jameskan1011/EMG-Controlled-Prosthetic-Hand/3D model/plunger/socket.SLDPRT

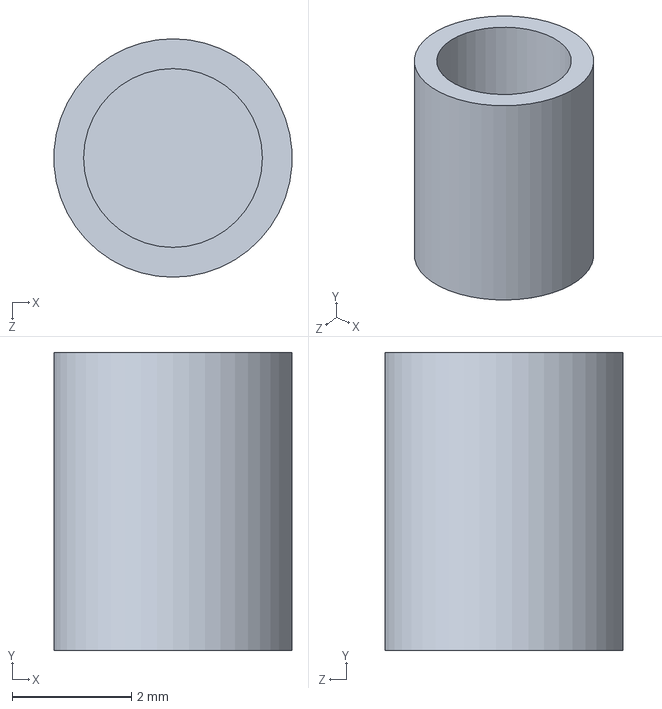
[picture p16: CAD file, 2025-07-29]
3D model/plunger/socket.SLDPRT
3.99 x 5.00 x 4.00 mm
