jameskan1011/EMG-Controlled-Prosthetic-Hand/3D model/thumb/bambu/Thump1.3MF

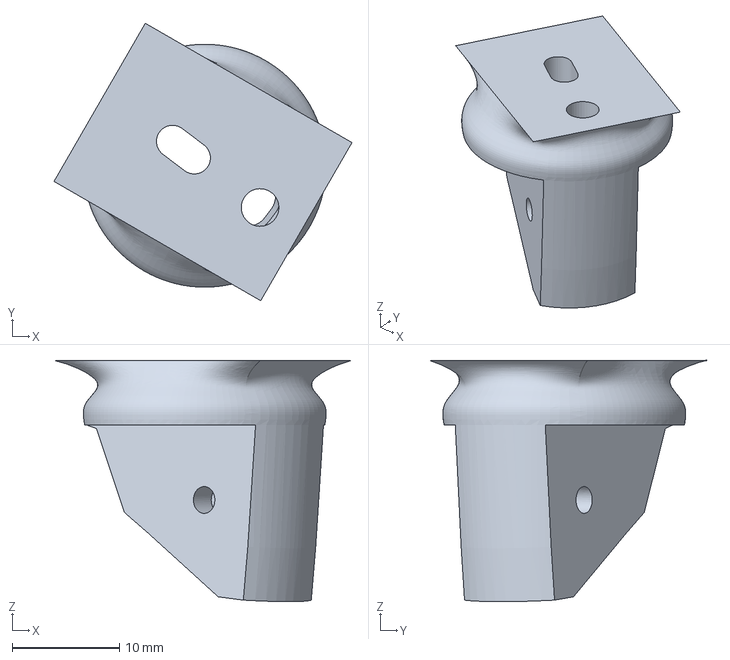
[picture p17: CAD file, 2025-07-29]
3D model/thumb/bambu/Thump1.3MF
27.7 x 25.8 x 22.5 mm
