jameskan1011/EMG-Controlled-Prosthetic-Hand/3D model/thumb/thump4.SLDPRT

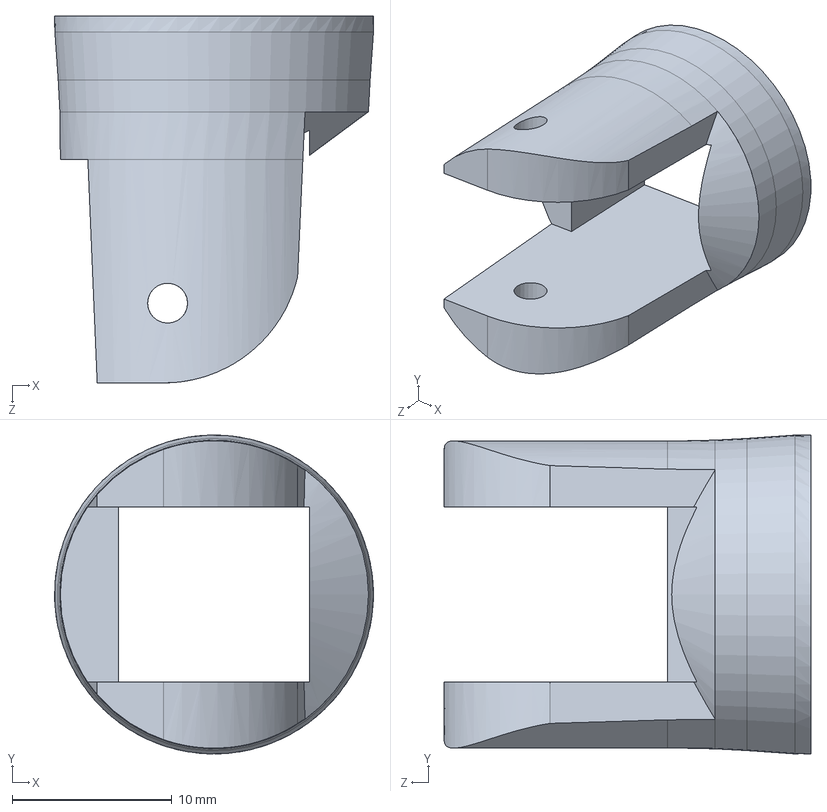
[picture p18: CAD file, 2025-07-29]
3D model/thumb/thump4.SLDPRT
20.0 x 20.0 x 23.0 mm
