jameskan1011/EMG-Controlled-Prosthetic-Hand/3D model/2051_servo_tower-pro-sg90.pk2.SLDPRT

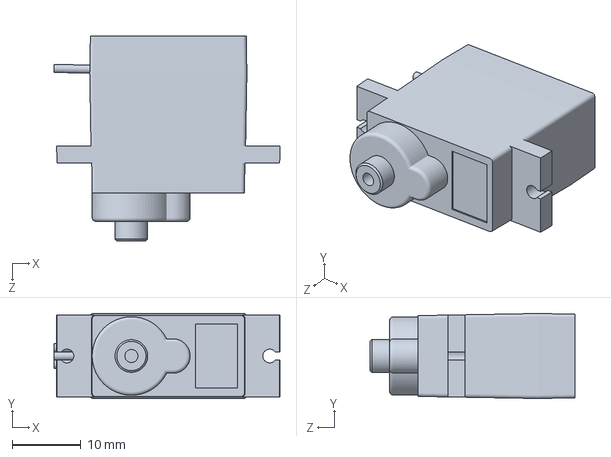
[picture p19: CAD file, 2025-07-29]
3D model/2051_servo_tower-pro-sg90.pk2.SLDPRT
32.9 x 12.4 x 29.8 mm
