jameskan1011/EMG-Controlled-Prosthetic-Hand/3D model/ESP32_enclosure/ESP32_enclosure.SLDPRT

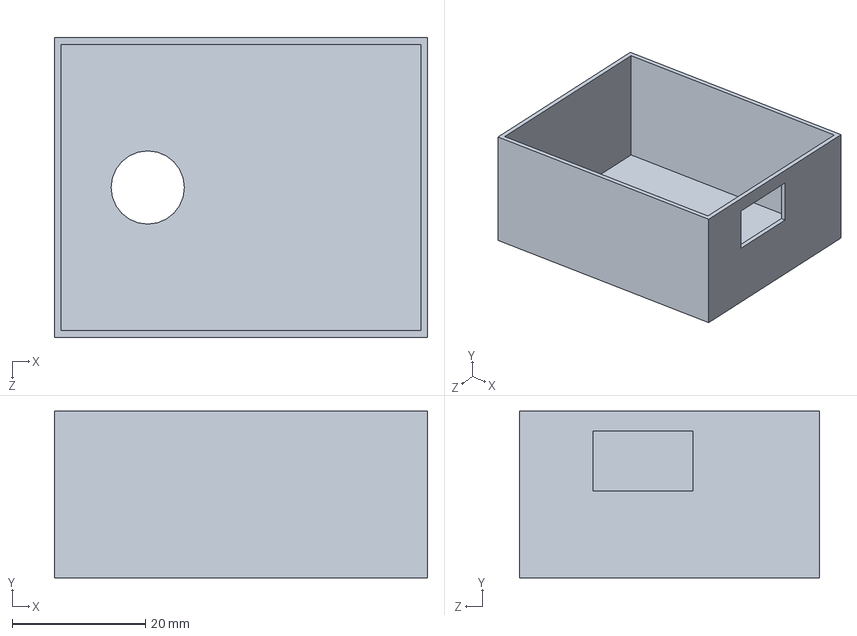
[picture p20: CAD file, 2025-07-29]
3D model/ESP32_enclosure/ESP32_enclosure.SLDPRT
56.0 x 25.0 x 45.0 mm
