jameskan1011/EMG-Controlled-Prosthetic-Hand/3D model/pinky/pinky3.SLDPRT

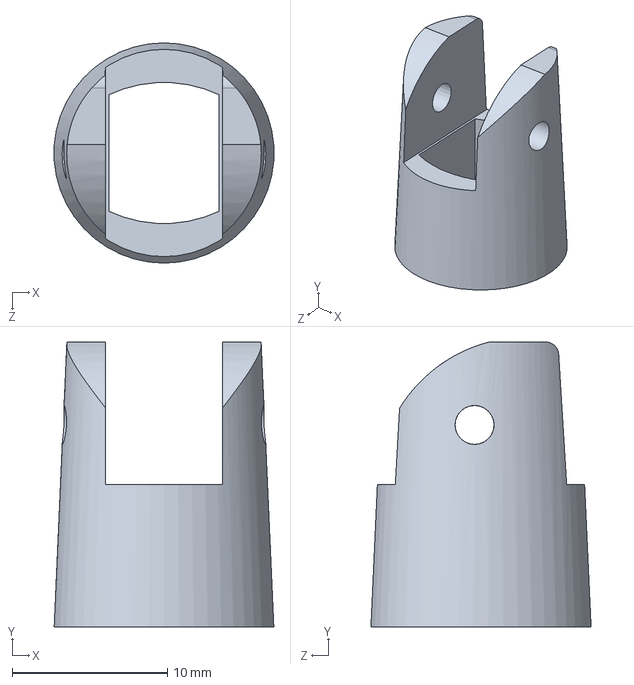
[picture p21: CAD file, 2025-07-29]
3D model/pinky/pinky3.SLDPRT
14.1 x 18.3 x 14.2 mm
