jameskan1011/EMG-Controlled-Prosthetic-Hand/3D model/thumb/thump6.SLDPRT

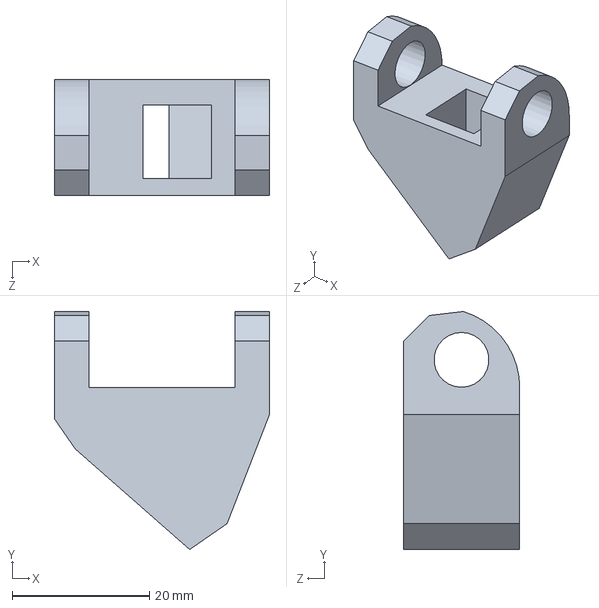
[picture p22: CAD file, 2025-07-29]
3D model/thumb/thump6.SLDPRT
31.4 x 34.7 x 17.0 mm
