jameskan1011/EMG-Controlled-Prosthetic-Hand/3D model/Index/bambu/index1_TPU_V2.3MF

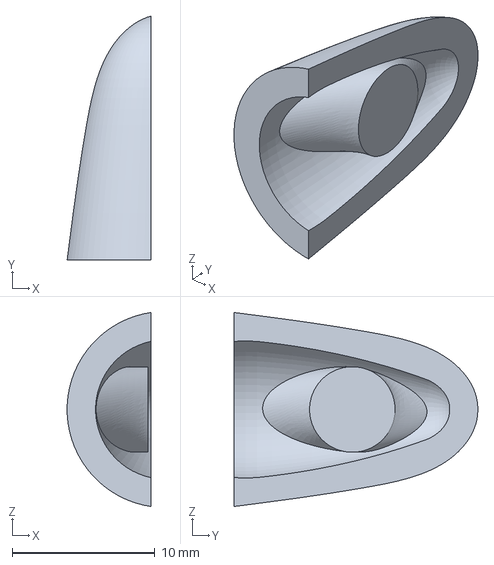
[picture p23: CAD file, 2025-07-29]
3D model/Index/bambu/index1_TPU_V2.3MF
5.87 x 17.1 x 13.6 mm
