jameskan1011/EMG-Controlled-Prosthetic-Hand/3D model/Index/index6.SLDPRT

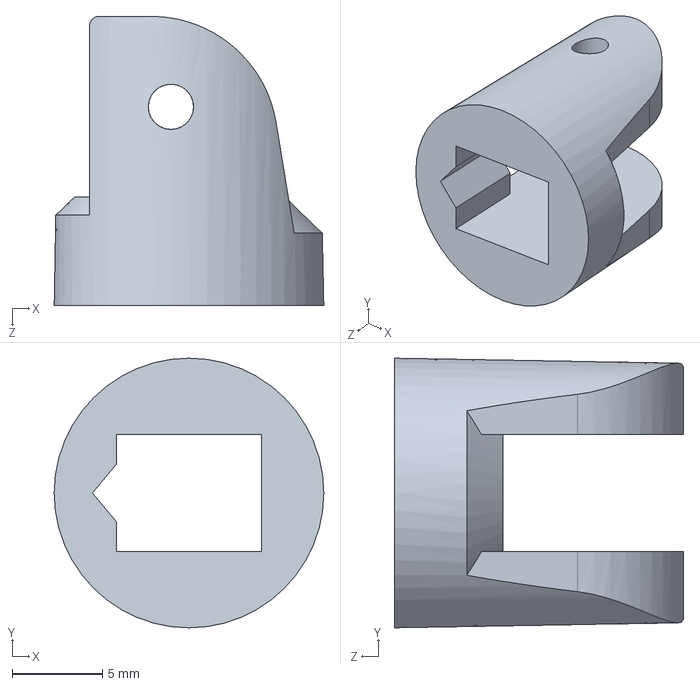
[picture p24: CAD file, 2025-07-29]
3D model/Index/index6.SLDPRT
14.9 x 14.9 x 16.0 mm
