jameskan1011/EMG-Controlled-Prosthetic-Hand/3D model/middle/middle4.SLDPRT

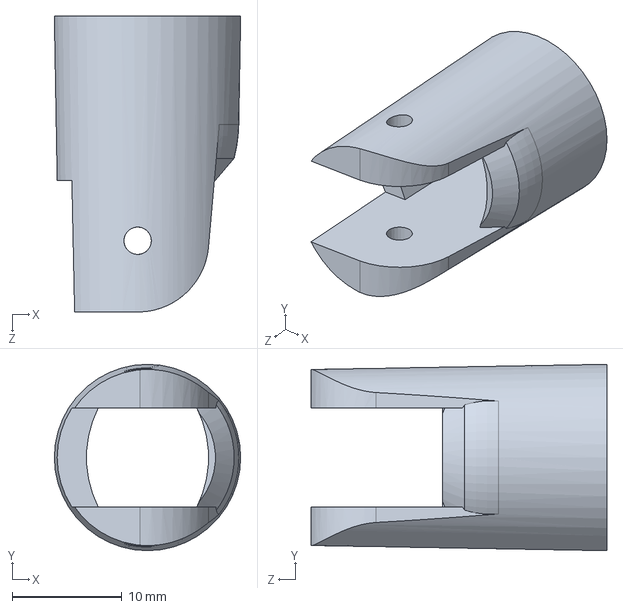
[picture p25: CAD file, 2025-07-29]
3D model/middle/middle4.SLDPRT
17.0 x 17.0 x 27.0 mm
