jameskan1011/EMG-Controlled-Prosthetic-Hand/3D model/palm_v2.SLDPRT

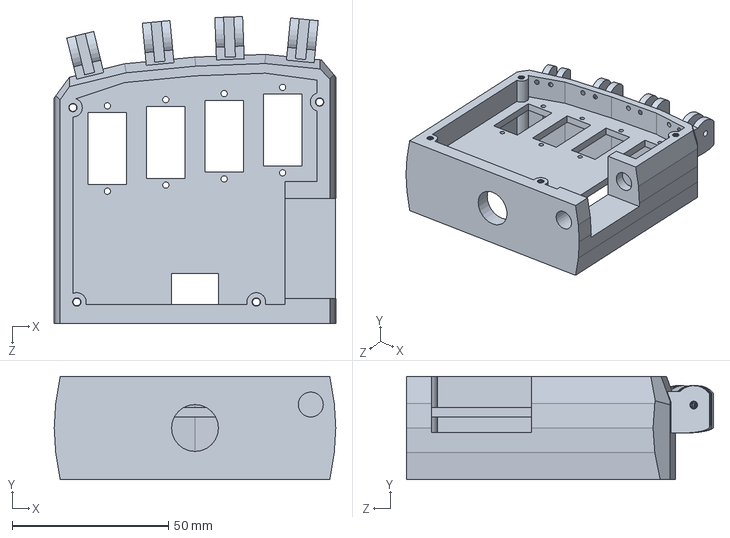
[picture p26: CAD file, 2025-07-29]
3D model/palm_v2.SLDPRT
90.0 x 33.0 x 98.1 mm
