jameskan1011/EMG-Controlled-Prosthetic-Hand/3D model/pinky/pinky1_tpu.SLDPRT

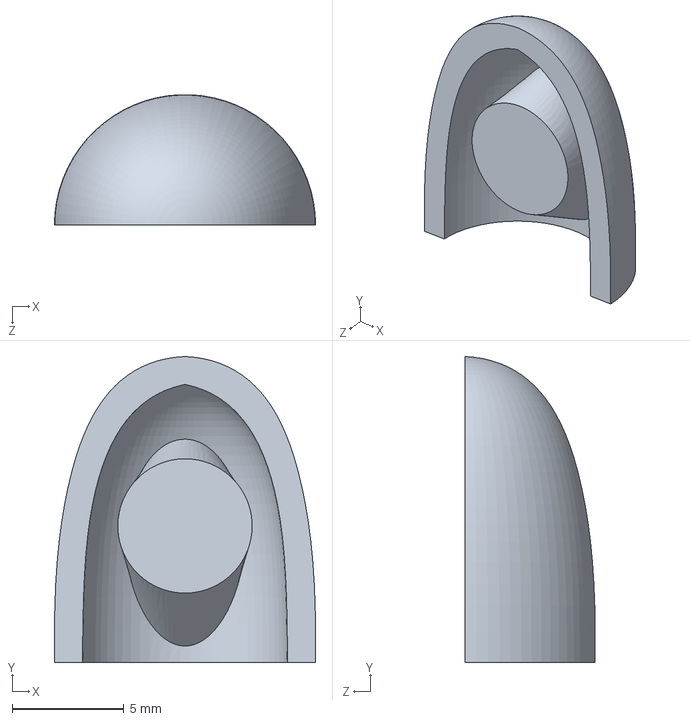
[picture p27: CAD file, 2025-07-29]
3D model/pinky/pinky1_tpu.SLDPRT
11.7 x 13.7 x 5.83 mm
