jameskan1011/EMG-Controlled-Prosthetic-Hand/3D model/thumb/Thump1_v1.SLDPRT

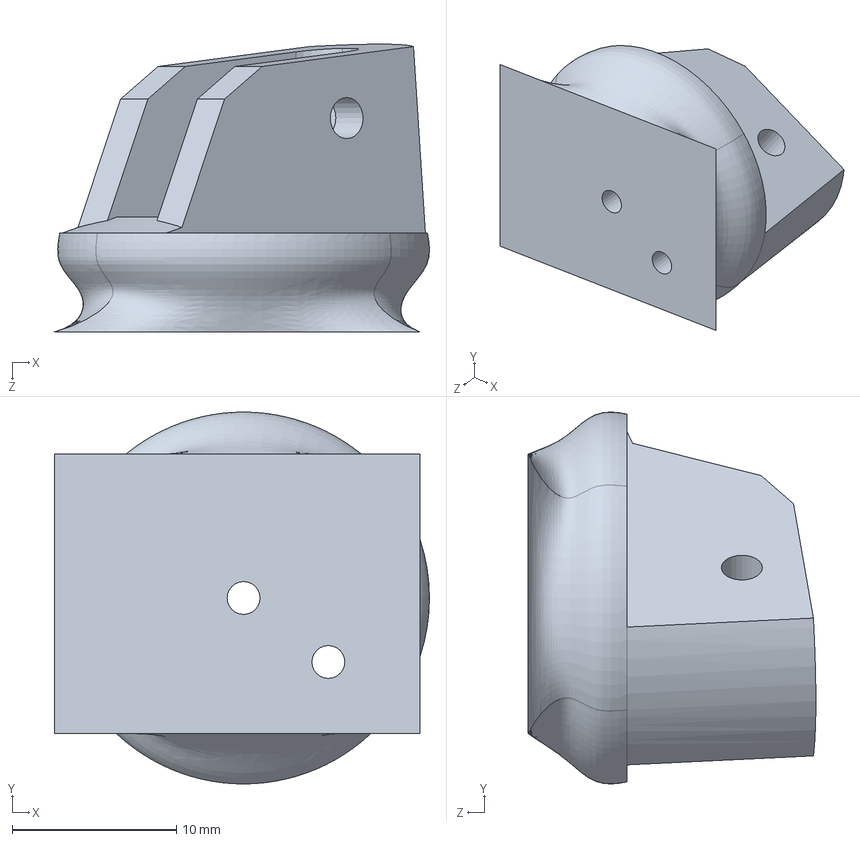
[picture p29: CAD file, 2025-07-29]
3D model/thumb/Thump1_v1.SLDPRT
22.8 x 22.6 x 17.5 mm
