jameskan1011/EMG-Controlled-Prosthetic-Hand/3D model/middle/middle1.SLDPRT

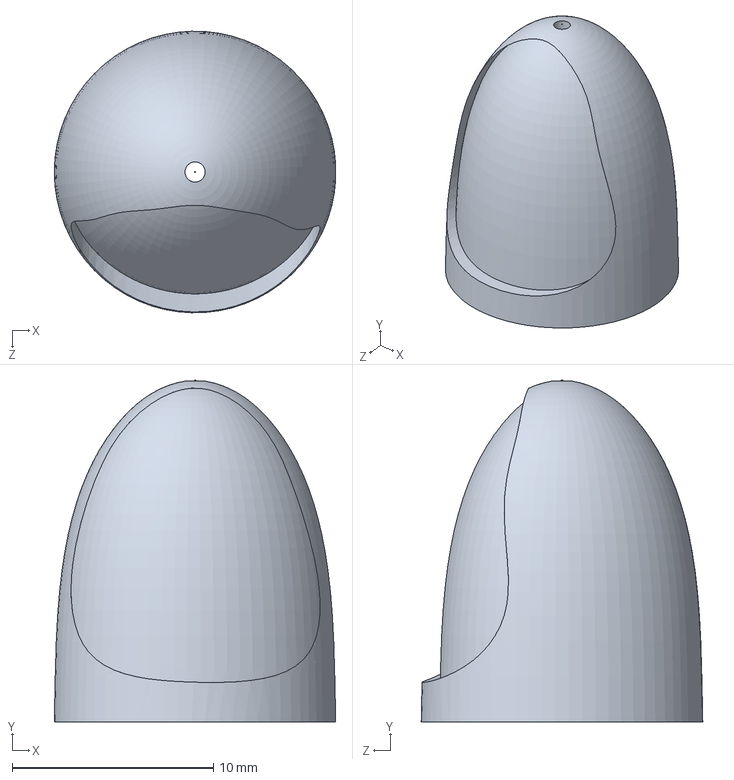
[picture p30: CAD file, 2025-07-29]
3D model/middle/middle1.SLDPRT
14.0 x 17.0 x 14.0 mm
