jameskan1011/EMG-Controlled-Prosthetic-Hand/3D model/pinky/pinky2_v2_longer.SLDPRT

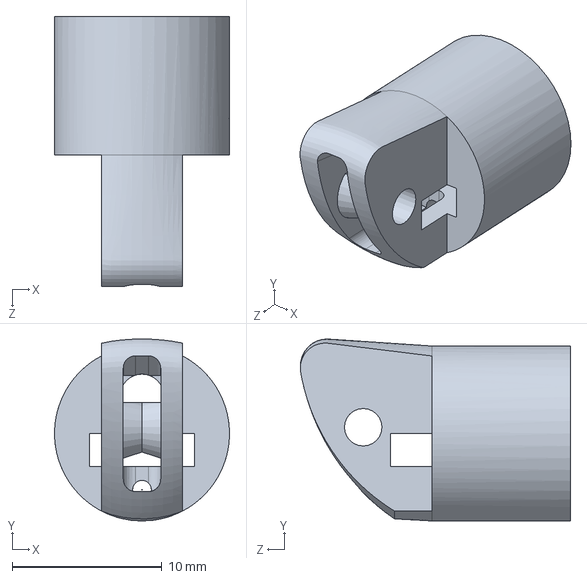
[picture p31: CAD file, 2025-07-29]
3D model/pinky/pinky2_v2_longer.SLDPRT
11.7 x 12.1 x 18.0 mm
