jameskan1011/EMG-Controlled-Prosthetic-Hand/3D model/servo horn_v2.SLDPRT

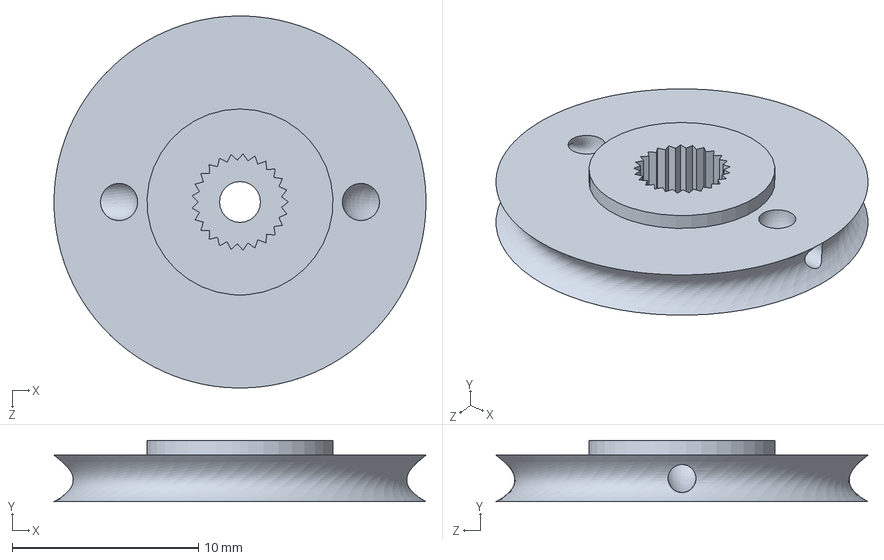
[picture p32: CAD file, 2025-07-29]
3D model/servo horn_v2.SLDPRT
20.0 x 3.30 x 20.0 mm
