jameskan1011/EMG-Controlled-Prosthetic-Hand/3D model/Index/bambu/index1_modifiled.3MF

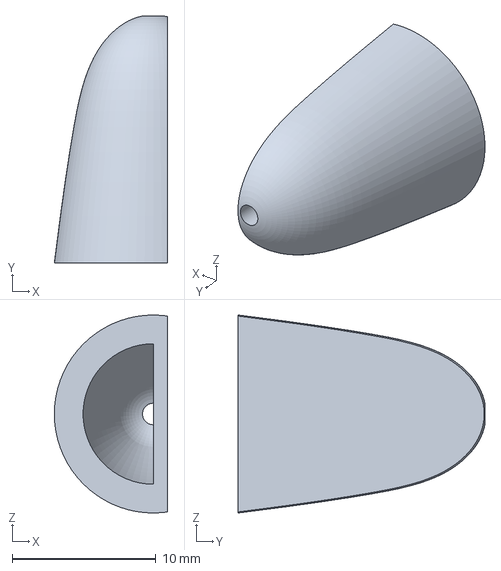
[picture p33: CAD file, 2025-07-29]
3D model/Index/bambu/index1_modifiled.3MF
7.88 x 17.2 x 13.8 mm
