jameskan1011/EMG-Controlled-Prosthetic-Hand/3D model/pinky/pinky6.SLDPRT

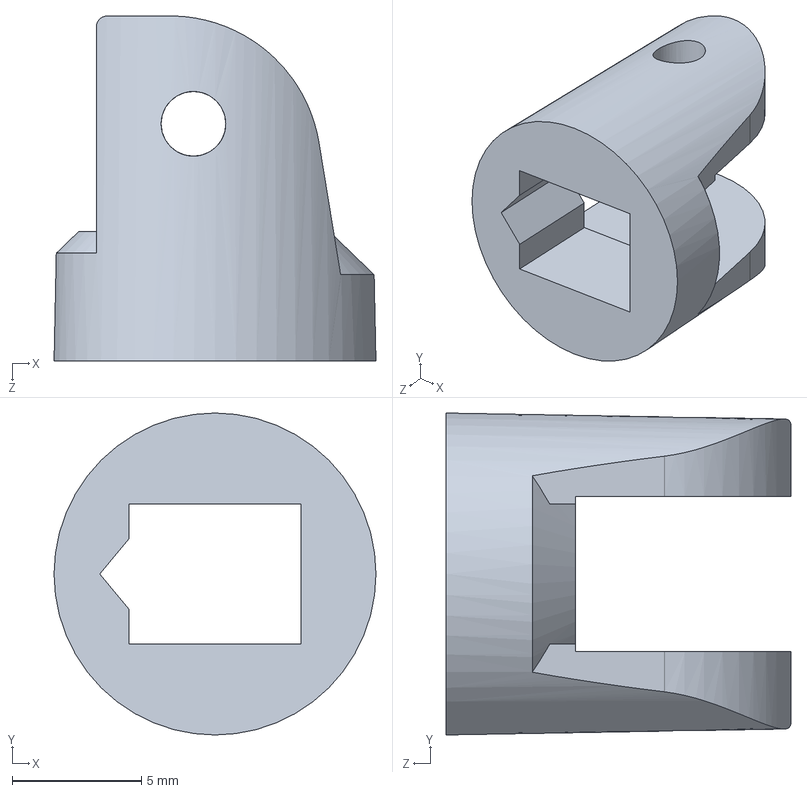
[picture p34: CAD file, 2025-07-29]
3D model/pinky/pinky6.SLDPRT
12.4 x 12.4 x 13.3 mm
