jameskan1011/EMG-Controlled-Prosthetic-Hand/3D model/thumb/bambu/thump0_tpu.3MF

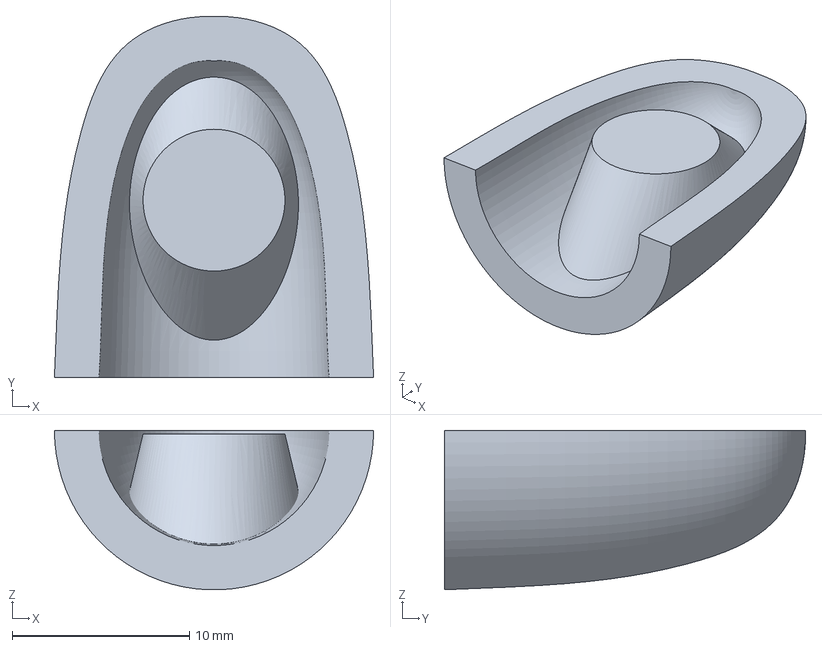
[picture p35: CAD file, 2025-07-29]
3D model/thumb/bambu/thump0_tpu.3MF
18.0 x 20.4 x 8.99 mm
