jameskan1011/EMG-Controlled-Prosthetic-Hand/3D model/wrist.SLDPRT

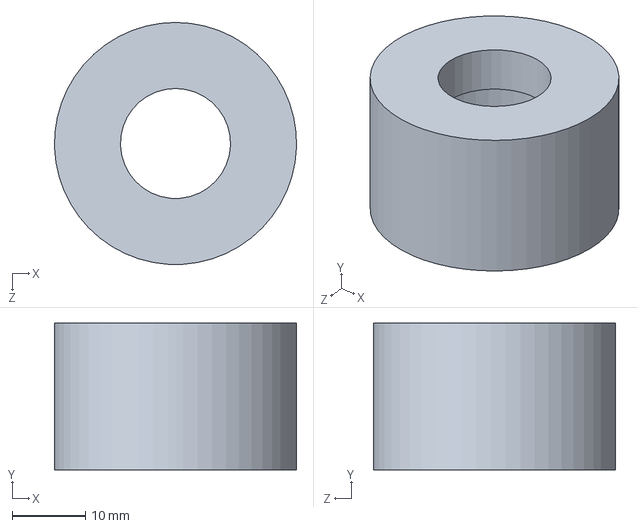
[picture p36: CAD file, 2025-07-29]
3D model/wrist.SLDPRT
33.0 x 20.0 x 33.0 mm
