jameskan1011/EMG-Controlled-Prosthetic-Hand/3D model/pinky/pinky5.SLDPRT

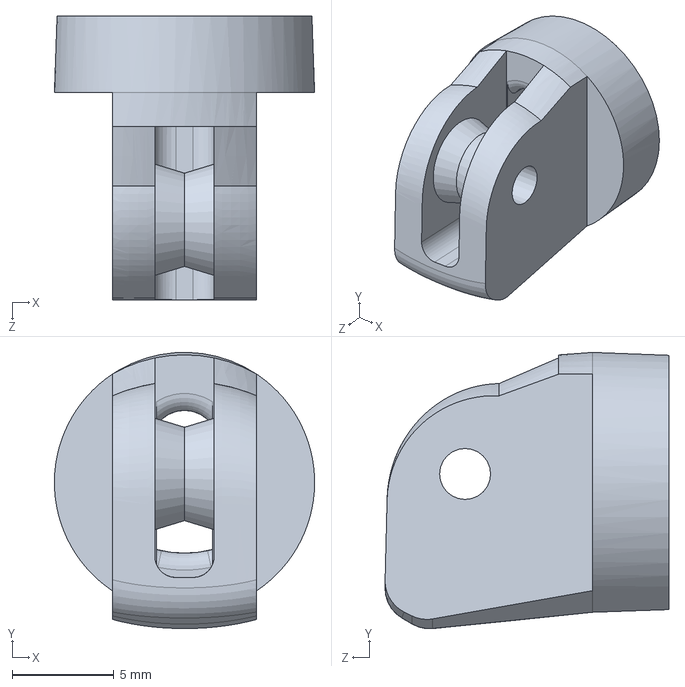
[picture p37: CAD file, 2025-07-29]
3D model/pinky/pinky5.SLDPRT
12.8 x 13.5 x 13.9 mm
