jameskan1011/EMG-Controlled-Prosthetic-Hand/3D model/thumb/bambu/thump2.3MF

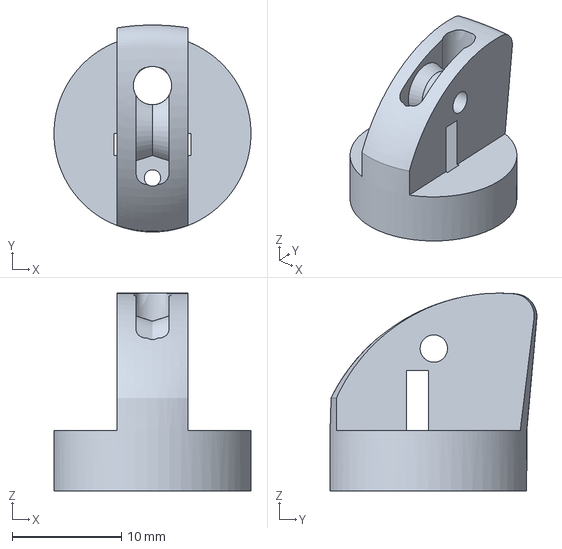
[picture p38: CAD file, 2025-07-29]
3D model/thumb/bambu/thump2.3MF
18.0 x 18.9 x 18.1 mm
