jameskan1011/EMG-Controlled-Prosthetic-Hand/3D model/wrist1.SLDPRT

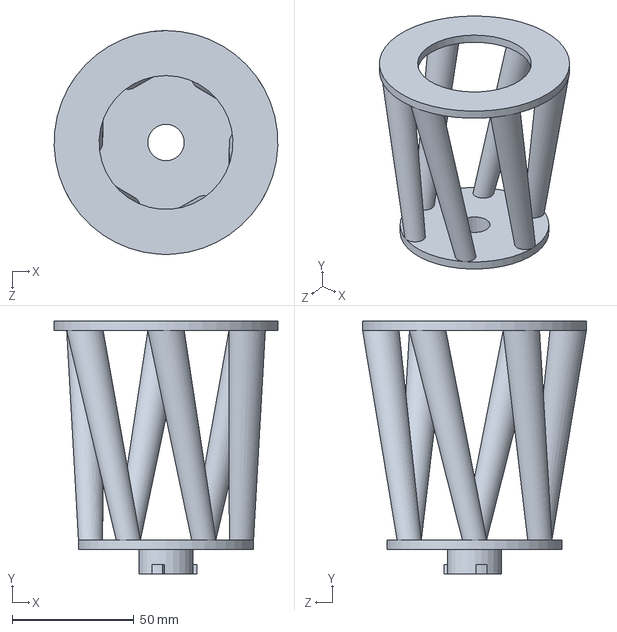
[picture p39: CAD file, 2025-07-29]
3D model/wrist1.SLDPRT
91.9 x 104.0 x 92.0 mm
