jameskan1011/EMG-Controlled-Prosthetic-Hand/3D model/Index/bambu/index1_TPU.3MF

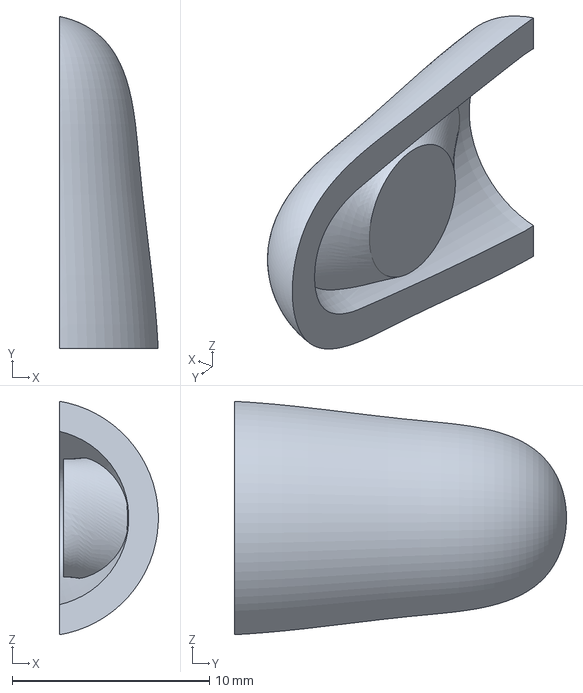
[picture p40: CAD file, 2025-07-29]
3D model/Index/bambu/index1_TPU.3MF
4.99 x 16.8 x 11.8 mm
