jameskan1011/EMG-Controlled-Prosthetic-Hand/3D model/Index/index1.SLDPRT

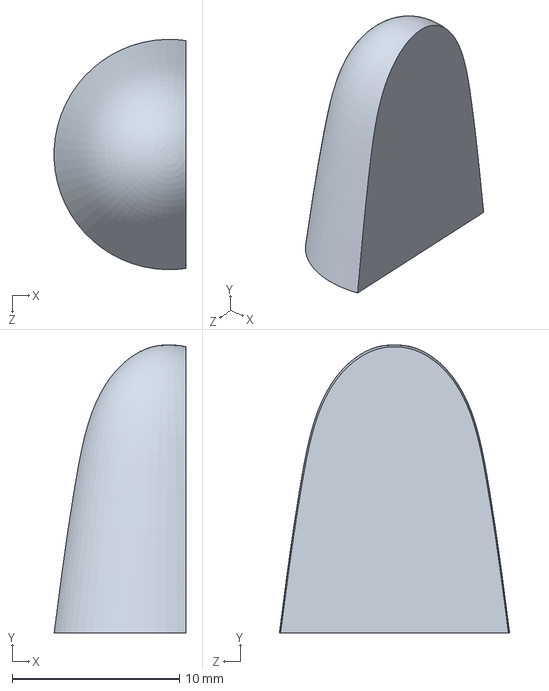
[picture p41: CAD file, 2025-07-29]
3D model/Index/index1.SLDPRT
7.87 x 17.2 x 13.8 mm
