jameskan1011/EMG-Controlled-Prosthetic-Hand/3D model/palm_top.SLDPRT

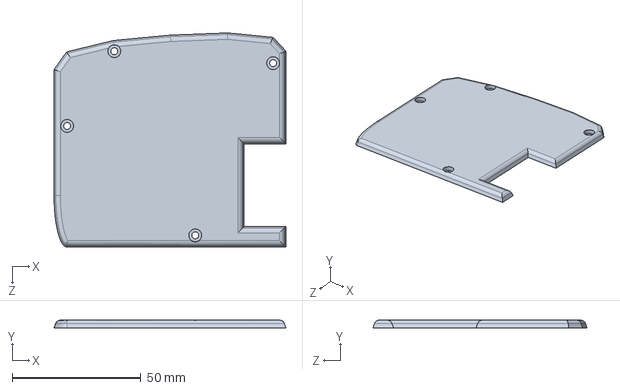
[picture p42: CAD file, 2025-07-29]
3D model/palm_top.SLDPRT
90.0 x 3.00 x 83.1 mm
