jameskan1011/EMG-Controlled-Prosthetic-Hand/3D model/pinky/pinky1.SLDPRT

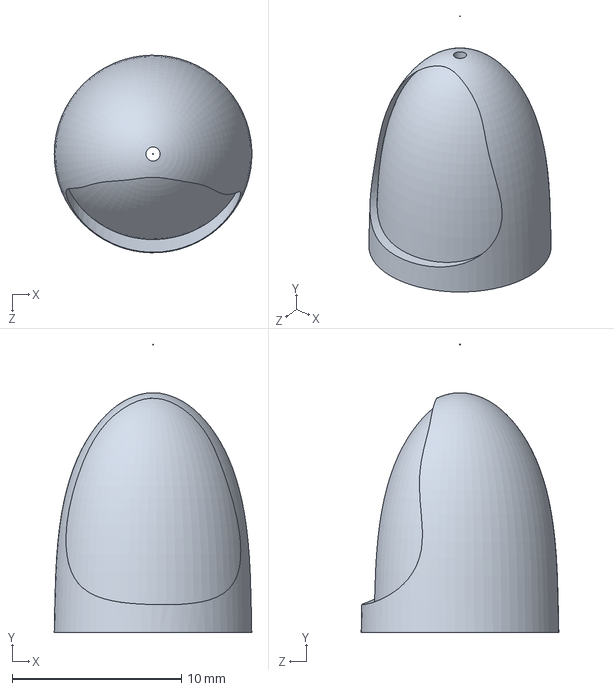
[picture p43: CAD file, 2025-07-29]
3D model/pinky/pinky1.SLDPRT
11.7 x 17.0 x 11.7 mm
