jameskan1011/EMG-Controlled-Prosthetic-Hand/3D model/thumb/bambu/thumb_link.3MF

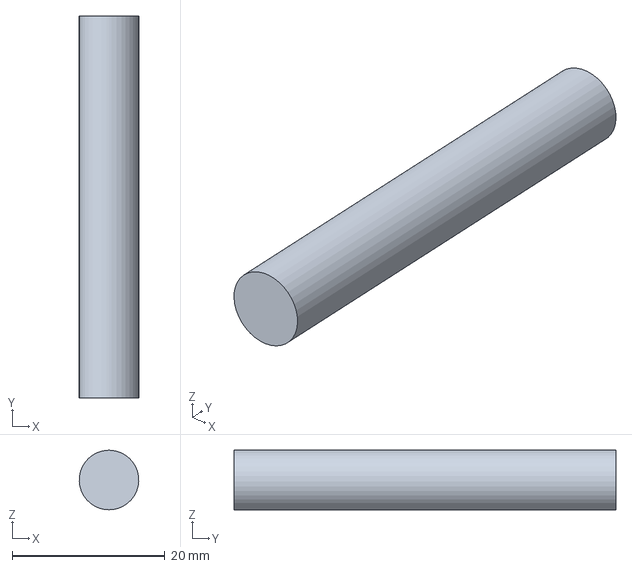
[picture p44: CAD file, 2025-07-29]
3D model/thumb/bambu/thumb_link.3MF
7.79 x 50.0 x 7.80 mm
