jameskan1011/EMG-Controlled-Prosthetic-Hand/3D model/Index/index1_TPU.SLDPRT

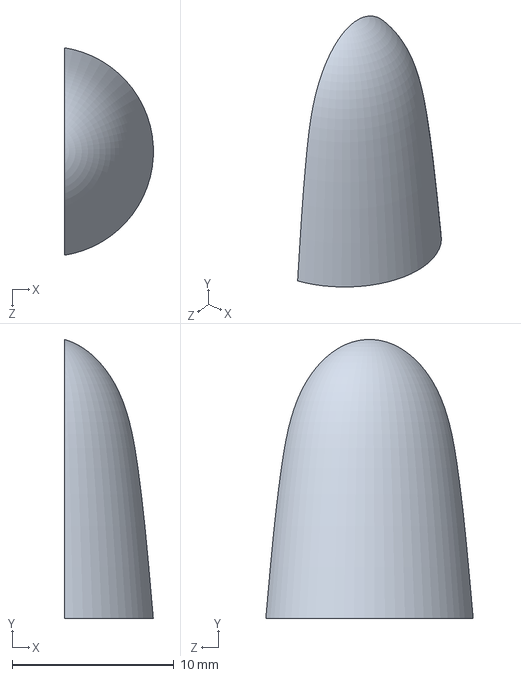
[picture p45: CAD file, 2025-07-29]
3D model/Index/index1_TPU.SLDPRT
5.49 x 17.3 x 12.8 mm
