jameskan1011/EMG-Controlled-Prosthetic-Hand/3D model/mg90_serv_inmoov.SLDPRT

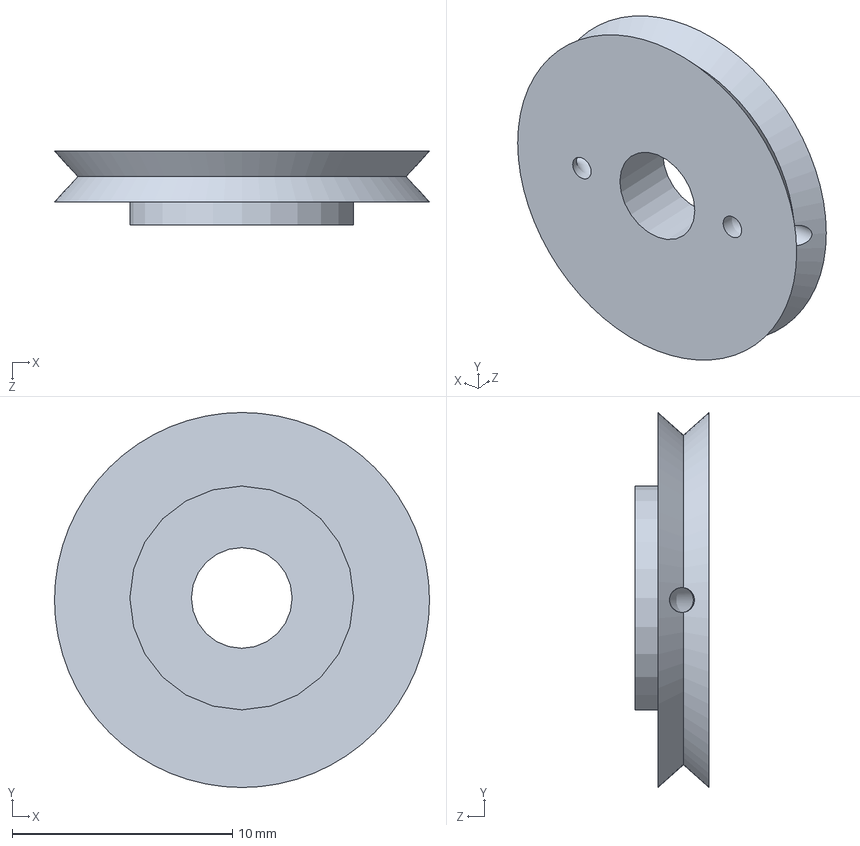
[picture p46: CAD file, 2025-07-29]
3D model/mg90_serv_inmoov.SLDPRT
17.0 x 17.0 x 3.36 mm
