jameskan1011/EMG-Controlled-Prosthetic-Hand/3D model/pinky/pinky1_v1.SLDPRT

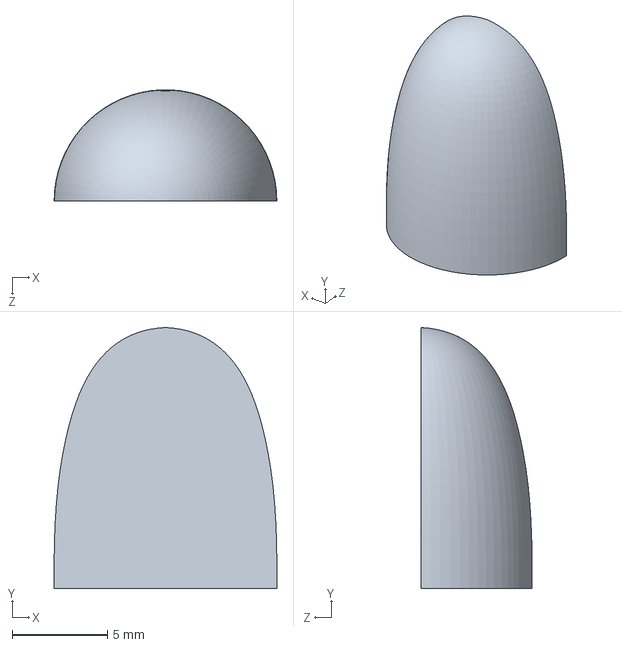
[picture p47: CAD file, 2025-07-29]
3D model/pinky/pinky1_v1.SLDPRT
11.7 x 13.7 x 5.83 mm
