jameskan1011/EMG-Controlled-Prosthetic-Hand/3D model/thumb/bambu/thump5.3MF

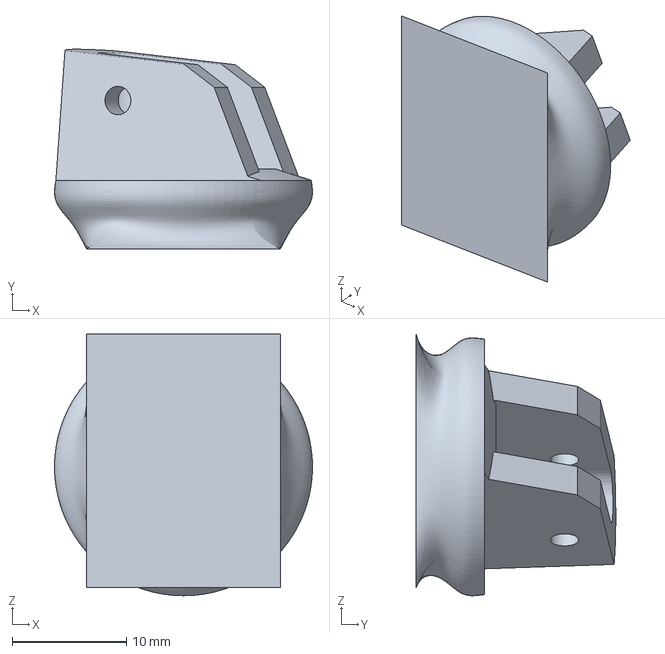
[picture p48: CAD file, 2025-07-29]
3D model/thumb/bambu/thump5.3MF
22.6 x 17.5 x 22.9 mm
